jean-claudeF/SOMCA/KiCAD/somca_03.kicad_sch

## KiCad design KiCAD/somca_03.kicad_sch (2026-02-25)

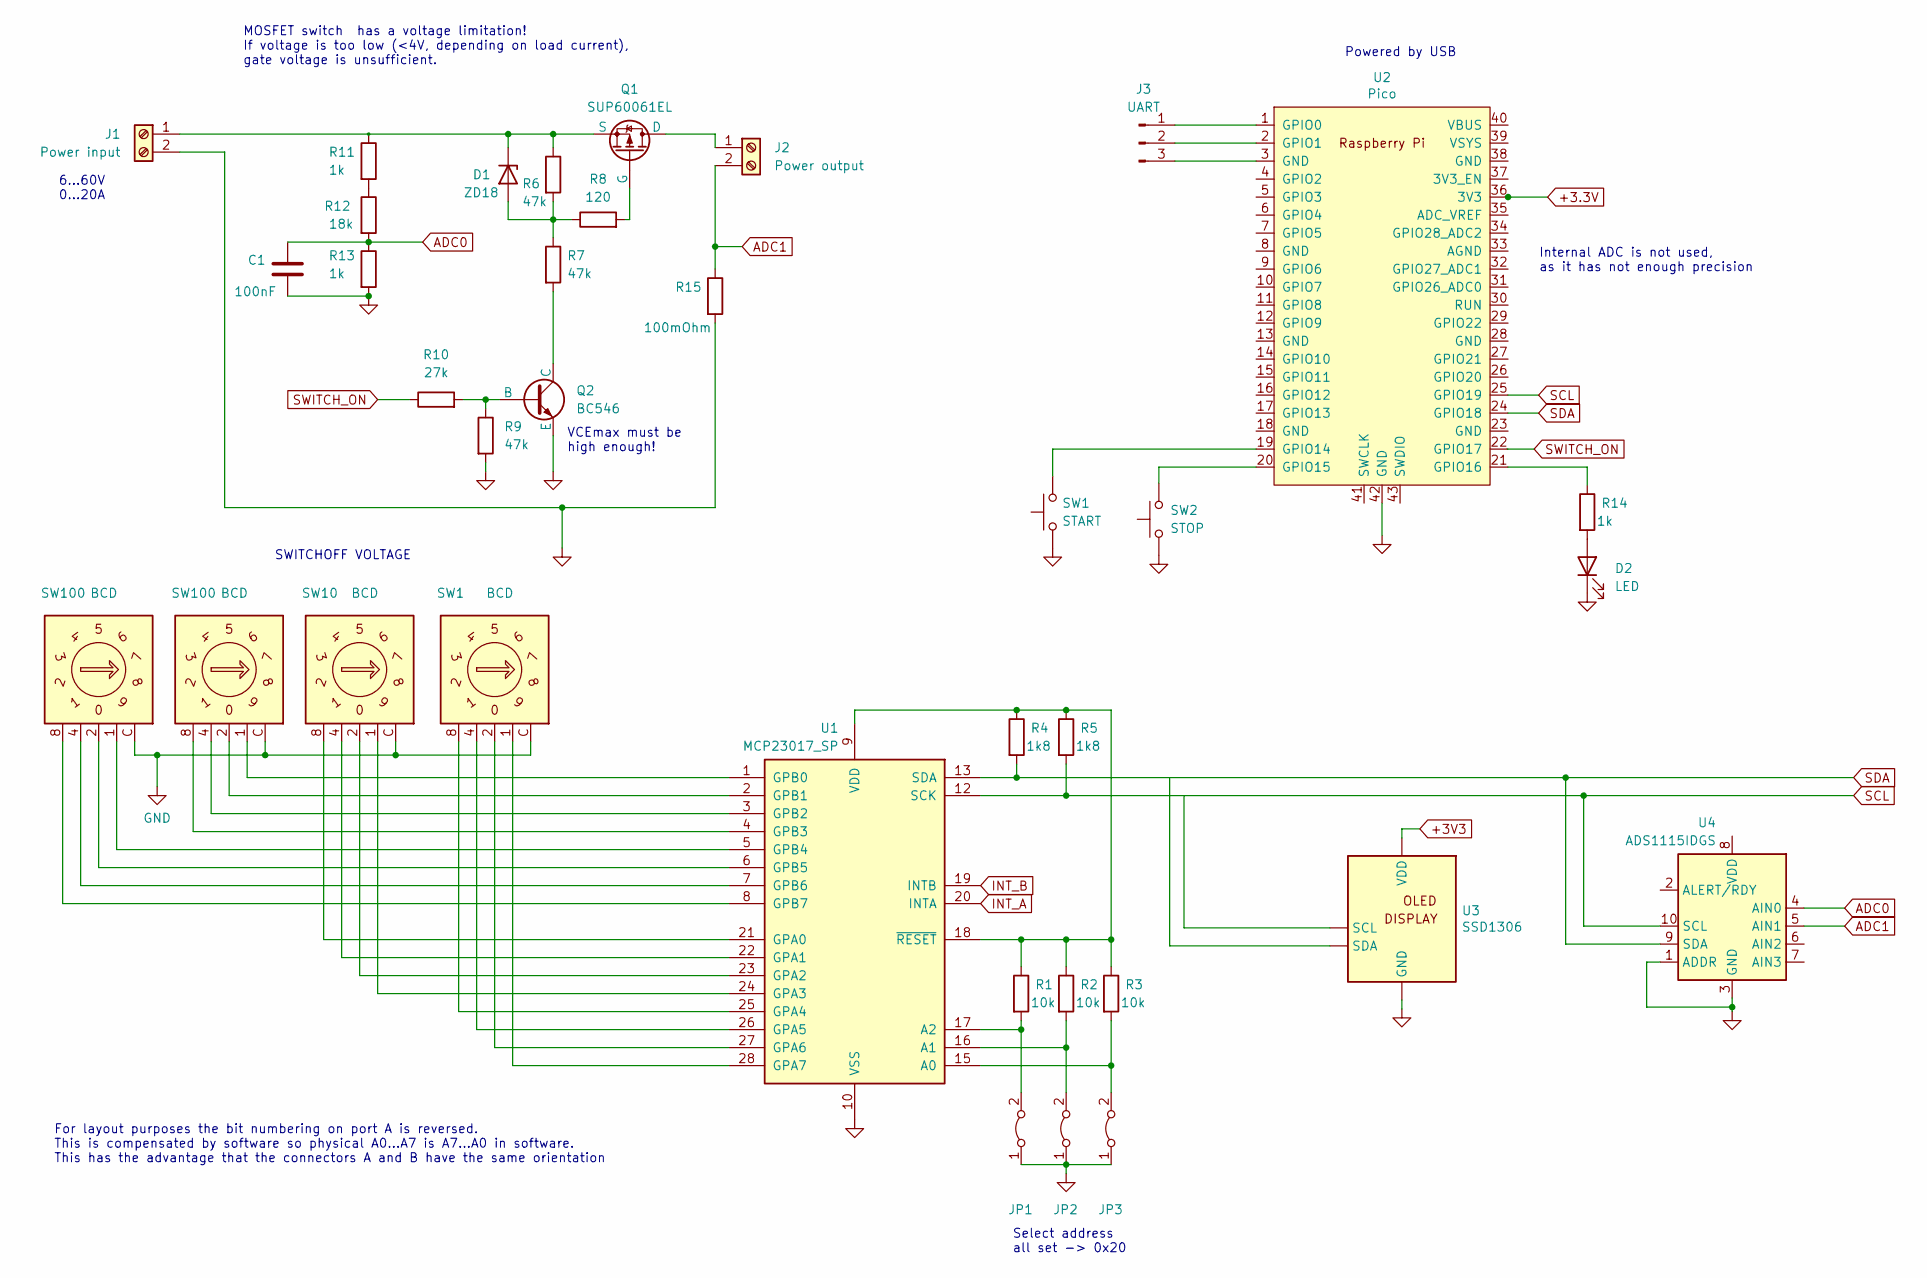
[picture p7: schematic somca_03.kicad_sch]

Parts:
C1: 100nF
D1: ZD18
D2: LED
J1: Power input
J2: Power output
J3: UART
JP1, JP2, JP3: (no value)
Q1: SUP60061EL
Q2: BC546
R1, R2, R3: 10k
R4, R5: 1k8
R6, R7, R9: 47k
R8: 120
R10: 27k
R11, R13, R14: 1k
R12: 18k
R15: 100mOhm
SW1: START
SW2: STOP
SW10, SW100: BCD
U1: MCP23017_SP; DIP-28_W7.62mm
U2: Pico; RPi_Pico_SMD_TH
U3: SSD1306
U4: ADS1115IDGS; TSSOP-10_3x3mm_P0.5mm

Connections:
+3.3V: U2.36 (3V3)
+3V3: U3.8 (VDD)
ADC0: C1.1, R12.2, R13.1, U4.4 (AIN0)
ADC1: J2.2, R15.1, U4.5 (AIN1)
GND: C1.2, D2.1 (K), J1.2, JP1.1 (A), JP2.1 (A), JP3.1 (A), Q2.3 (E), R9.2, R13.2, R15.2, SW1.1, SW1.C, SW2.1, SW10.C, SW100.C, U1.10 (VSS), U2.42 (GND), U3.3 (GND), U4.1 (ADDR), U4.3 (GND)
INT_A: U1.20 (INTA)
INT_B: U1.19 (INTB)
unnamed: D1.1 (K), J1.1, Q1.3 (S), R6.1, R11.1
unnamed: D1.2 (A), R6.2, R7.1, R8.1
unnamed: D2.2 (A), R14.2
unnamed: J2.1, Q1.1 (D)
unnamed: J3.1, U2.1 (GPIO0)
unnamed: J3.2, U2.2 (GPIO1)
unnamed: J3.3, U2.3 (GND)
unnamed: JP1.2 (B), R1.2, U1.17 (A2)
unnamed: JP2.2 (B), R2.2, U1.16 (A1)
unnamed: JP3.2 (B), R3.2, U1.15 (A0)
unnamed: Q1.2 (G), R8.2
unnamed: Q2.1 (C), R7.2
unnamed: Q2.2 (B), R9.1, R10.2
unnamed: R1.1, R2.1, R3.1, R4.1, R5.1, U1.9 (VDD), U1.18 (~RESET)
unnamed: R11.2, R12.1
unnamed: R14.1, U2.21 (GPIO16)
unnamed: SW1.1, U1.28 (GPA7)
unnamed: SW1.2, U1.27 (GPA6), U2.19 (GPIO14)
unnamed: SW1.4, U1.26 (GPA5)
unnamed: SW1.8, U1.25 (GPA4)
unnamed: SW2.2, U2.20 (GPIO15)
unnamed: SW10.1, U1.24 (GPA3)
unnamed: SW10.2, U1.23 (GPA2)
unnamed: SW10.4, U1.22 (GPA1)
unnamed: SW10.8, U1.21 (GPA0)
unnamed: SW100.1, U1.1 (GPB0), U1.5 (GPB4)
unnamed: SW100.2, U1.2 (GPB1), U1.6 (GPB5)
unnamed: SW100.4, U1.3 (GPB2), U1.7 (GPB6)
unnamed: SW100.8, U1.4 (GPB3), U1.8 (GPB7)
SCL: R5.2, U1.12 (SCK), U2.25 (GPIO19), U4.10 (SCL)
SDA: R4.2, U1.13 (SDA), U2.24 (GPIO18), U4.9 (SDA)
SWITCH_ON: R10.1

Notes on the sheet:
Select address all set -> 0x20
VCEmax must be high enough!
6...60V 0...20A
For layout purposes the bit numbering on port A is reversed. This is compensated by software so physical A0...A7 is A7...A0 in software. This has the advantage that the connectors A and B have the same orientation
SWITCHOFF VOLTAGE
MOSFET switch has a voltage limitation! If voltage is too low (<4V, depending on load current), gate voltage is unsufficient.
Internal ADC is not used, as it has not enough precision
Powered by USB
